TimGoll/sonoff_zbminir2_24Vmod/main_board_24V/main_board_24V.kicad_sch

## KiCad design main_board_24V/main_board_24V.kicad_sch (2026-01-13)

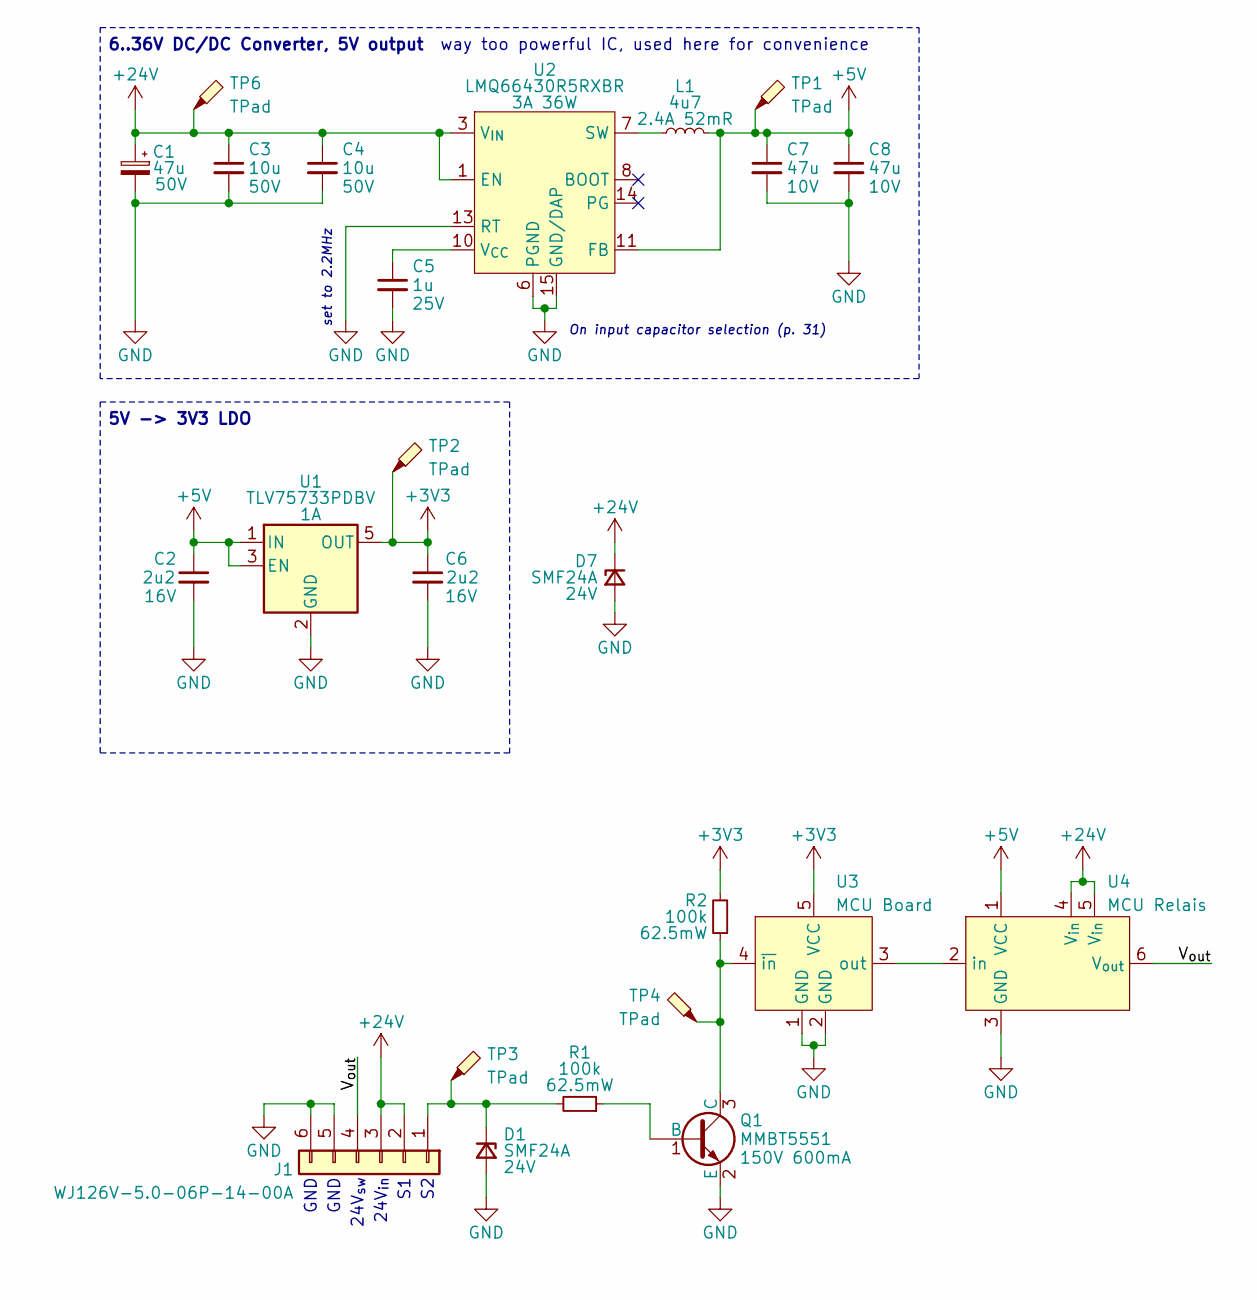
[picture p7: schematic main_board_24V.kicad_sch]

Parts:
C1: 47u; CP_Elec_6.3x7.7; Rating 50V; LCSC Part # C3349
C2, C6: 2u2; C_0603_1608Metric; Rating 16V; MPN Samsung CL10A225KO5LNW; LCSC Part # C23630
C3, C4: 10u; C_1206_3216Metric; Rating 50V; LCSC Part # C13585
C5: 1u; C_0402_1005Metric; Rating 25V; LCSC Part # C52923
C7, C8: 47u; C_1206_3216Metric; Rating 10V; LCSC Part # C96123
D1, D7: SMF24A; D_SOD-123F; Rating 24V; LCSC Part # C19077514
J1: WJ126V-5.0-06P-14-00A; TerminalBlock_MaiXu_MX126-5.0-06P_1x06_P5.00mm; JLC Part # C8379
L1: 4u7; L_Sunlord_SWPA4030S; Rating 2.4A 52mR; LCSC Part # C15269
Q1: MMBT5551; SOT-23; Rating 150V 600mA; LCSC Part # C2145
R1, R2: 100k; R_0402_1005Metric; Rating 62.5mW; LCSC Part # C25741
TP1, TP2, TP3, TP4, TP6: TPad; TestPoint_Pad_D1.0mm
U1: TLV75733PDBV; SOT-23-5; Rating 1A; MPN TI TLV75733PDBV; LCSC Part # C485517
U2: LMQ66430R5RXBR; TI_VQFN_15_EP; Rating 3A 36W; LCSC Part # C22440565
U3: MCU Board; pcb_mcu
U4: MCU Relais; pcb_relais

Connections:
+3V3: C6.1, R2.2, TP2.1, U1.5 (OUT), U3.5 (VCC)
+5V: C2.1, C7.1, C8.1, L1.2, TP1.1, U1.1 (IN), U1.3 (EN), U2.11 (FB), U4.1 (VCC)
+24V: C1.1, C3.1, C4.1, D7.1 (K), J1.2, J1.3, TP6.1, U2.1 (EN), U2.3 (V_{IN}), U4.4 (V_{in}), U4.5 (V_{in})
GND: C1.2, C2.2, C3.2, C4.2, C5.2, C6.2, C7.2, C8.2, D1.2 (A), D7.2 (A), J1.5, J1.6, Q1.2 (E), U1.2 (GND), U2.6 (PGND), U2.13 (RT), U2.15 (GND/DAP), U3.1 (GND), U3.2 (GND), U4.3 (GND)
unnamed: C5.1, U2.10 (V_{CC})
unnamed: D1.1 (K), J1.1, R1.2, TP3.1
unnamed: L1.1, U2.7 (SW)
unnamed: Q1.1 (B), R1.1
unnamed: Q1.3 (C), R2.1, TP4.1, U3.4 (~in)
unnamed: U3.3 (out), U4.2 (in)
V_{out}: J1.4, U4.6 (V_{out})

Notes on the sheet:
GND
5V -> 3V3 LDO
way too powerful IC, used here for convenience
set to 2.2MHz
6..36V DC/DC Converter, 5V output
24V_{sw}
24V_{in}
On input capacitor selection (p. 31)
